Iotnet/0G-LockControl-LSM110A/Hardware/certificacion-FCC/external-photos.pdf

FCC ID: 2AS8LLSM110A / IC: 25119-LSM110A

HCT CO., LTD
74, Seoicheon-ro 578beon-gil, Majang-myeon, Icheon-si, Gyeonggi-do, 17383, Rep. of KOREA
TEL : + 82 31 645 6300 | FAX : + 82 31 645 6401 | www.hct.co.kr

# EXTERNAL PHOTOGRAPHS

## ■ EXTERNAL PHOTO

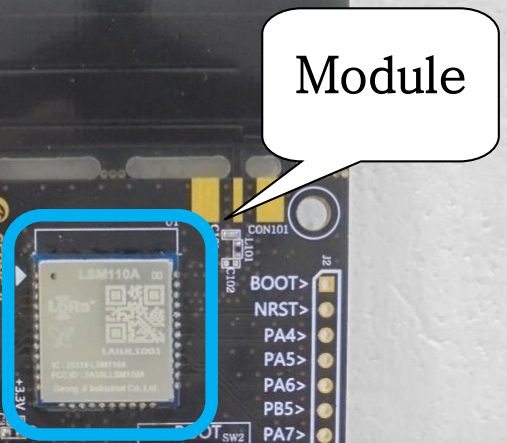
[picture p3: figure]
Module

## ■ EXTERNAL PHOTO

## ■ EXTERNAL PHOTO

## ■ EXTERNAL PHOTO

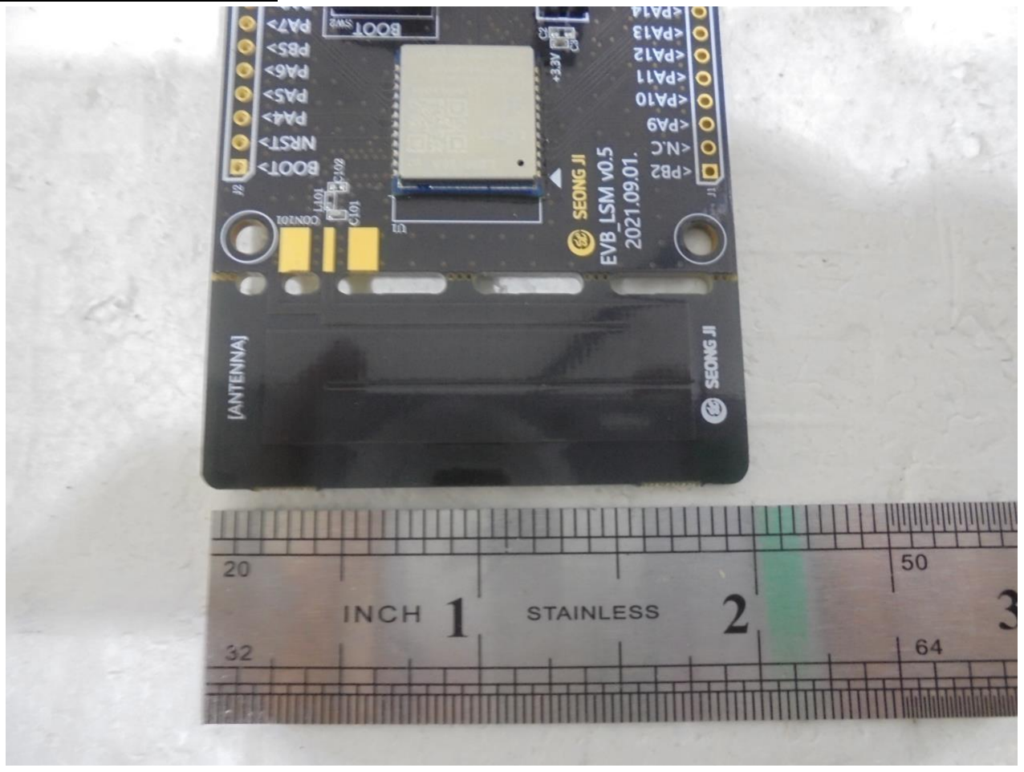
[picture p4: figure]
